TinyCircuits/TinyCircuits-TinyShield-BLE-ASD2116/images/ASD2116-R-Tutorial-Image-01.jpg

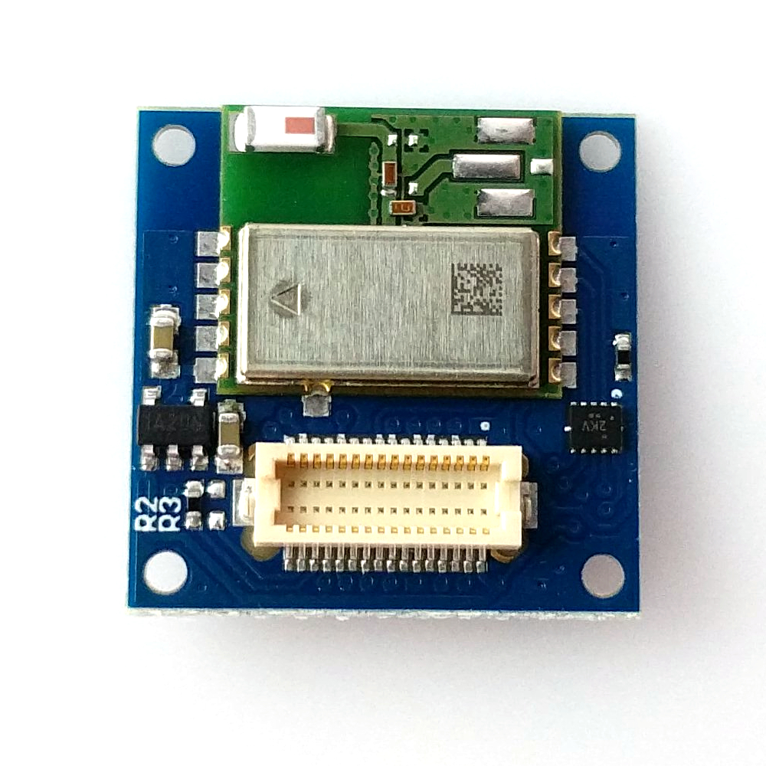
images/ASD2116-R-Tutorial-Image-01.jpg
