TinyCircuits/TinyCircuits-TinyShield-BLE-ASD2116/cad/TinyShield_STBLE_ASD2116_REV2-DETAILED_DRAWING-PNG.png

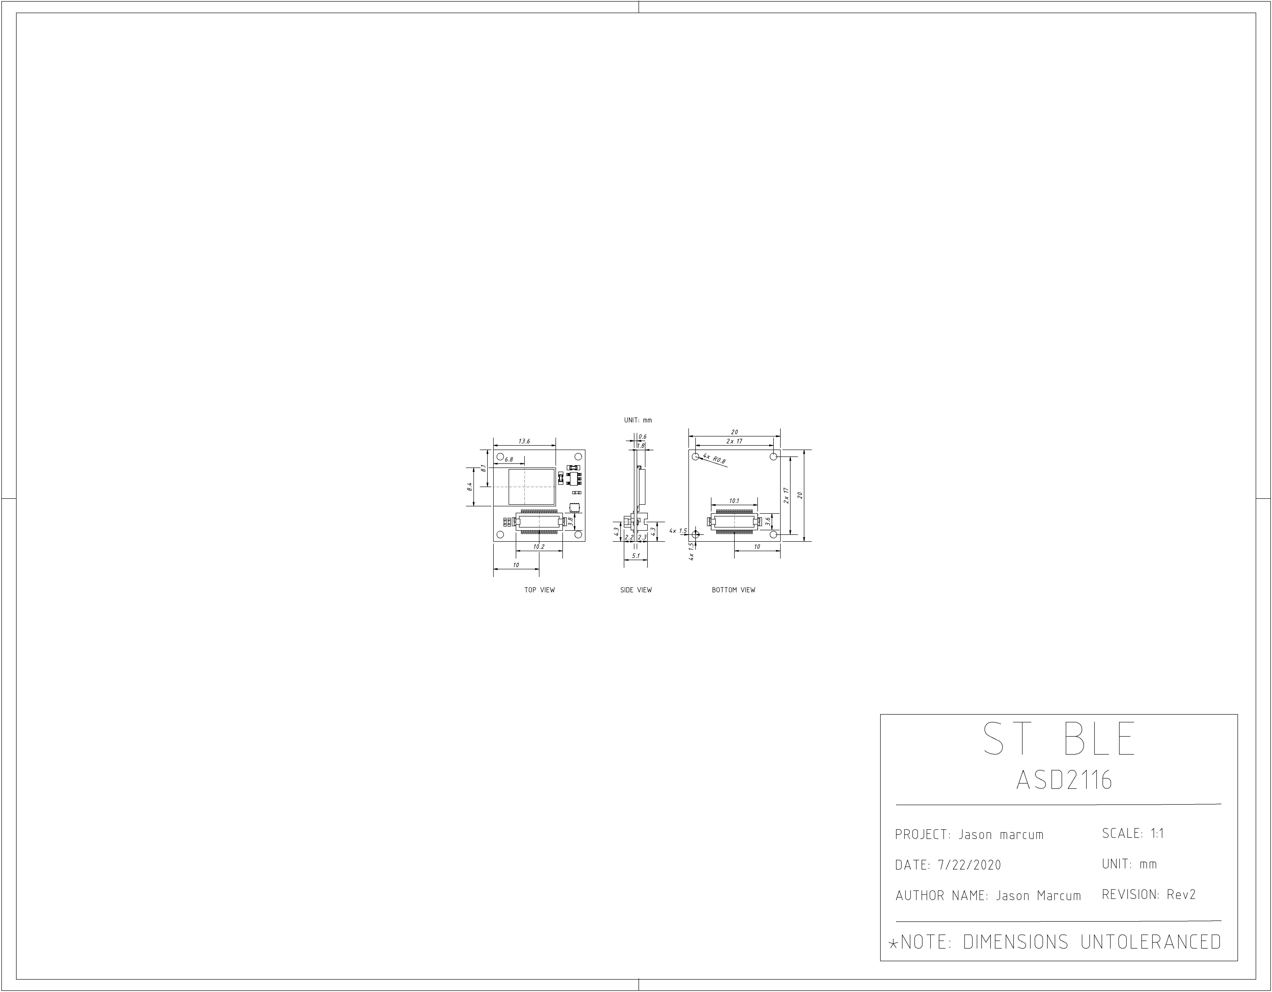
cad/TinyShield_STBLE_ASD2116_REV2-DETAILED_DRAWING-PNG.png
