TinyCircuits/TinyCircuits-TinyShield-BLE-ASD2116/images/ASD2116-Tutorial-Image-06.png

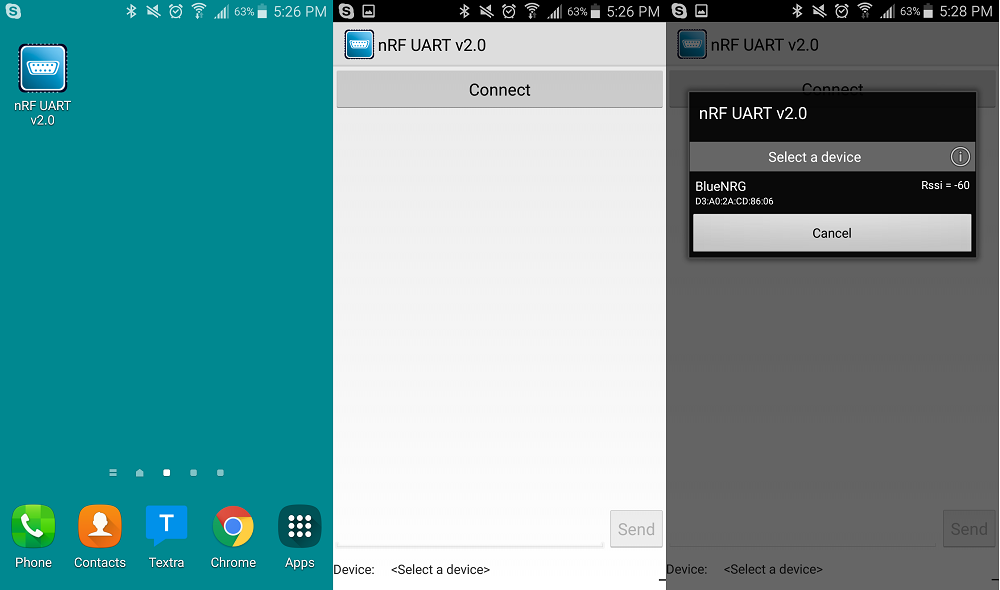
images/ASD2116-Tutorial-Image-06.png
