TinyCircuits/TinyCircuits-TinyShield-BLE-ASD2116/images/ASD2116-Tutorial-Image-09.png

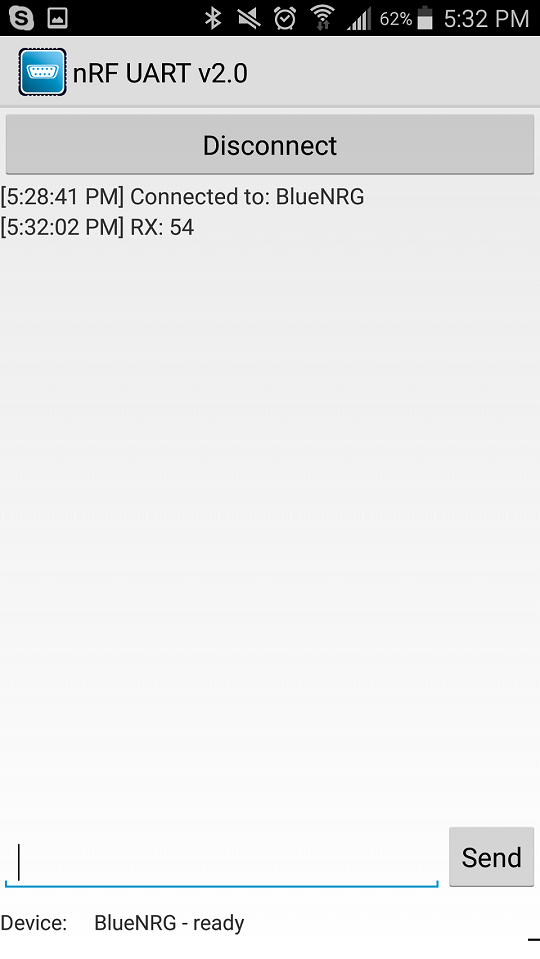
images/ASD2116-Tutorial-Image-09.png
